nodep/wht/WHTConfig/stdafx.h

#pragma once

#define _USE_MATH_DEFINES

// C
#include <cstdint>
#include <cassert>
#include <cmath>

// C++
#include <string>
#include <vector>
#include <map>
#include <iterator>
#include <algorithm>
#include <set>

// Windows
#define NOMINMAX
#include <windows.h>
#include <windowsx.h>
#include <commctrl.h>
#include <shellapi.h>
#include <shlobj.h>

// the core DirectX
/*
#ifdef _DEBUG
# define D3D_DEBUG_INFO
#endif
*/
#include <d3d9.h>
