nodep/wht/WHTConfig/wht_dongle.h

#pragma once

class WHTDongle
{
private:
	HANDLE	hDevice;

	void GetFeatureReportRaw(void* buffer, int report_size);
	void SetFeatureReportRaw(const void* buffer, int report_size);
	void GetInputReportRaw(void* buffer, int report_size);

	void ThrowException(const wchar_t* during, int report_id);

public:
	WHTDongle();
	~WHTDongle();

	bool Open();
	void Close();

	bool IsOpen() const
	{
		return hDevice != NULL;
	}
	
	template <class T>
	void GetFeatureReport(T& t)
	{
		GetFeatureReportRaw(&t, sizeof(t));
	}

	template <class T>
	void SetFeatureReport(const T& t)
	{
		SetFeatureReportRaw(&t, sizeof(t));
	}

	template <class T>
	void GetInputReport(T& t)
	{
		GetInputReportRaw(&t, sizeof(t));
	}

	bool ReadProtocolVersion(protocol_version_e& dongle_ver, protocol_version_e& tracker_ver);
};
